iotdevspot/encoder-debouncier-circuit-and-design-block/images/2.PNG

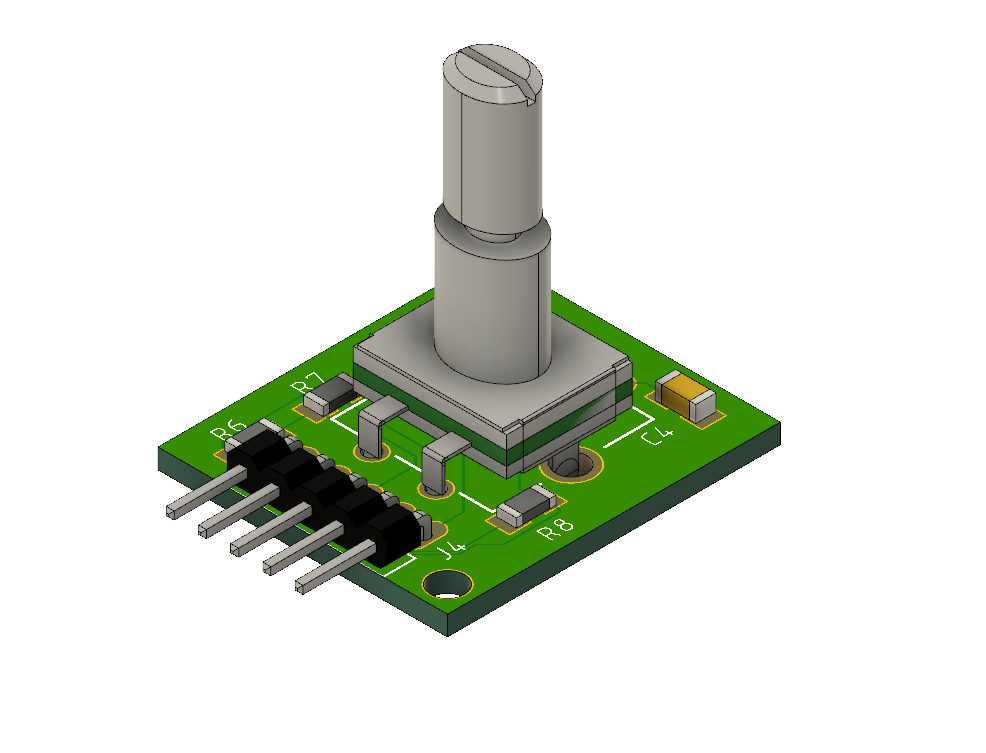
images/2.PNG
